LUMERIIX/FrequencyCounter/Documentation/Images/20180112_162158_HDR.jpg

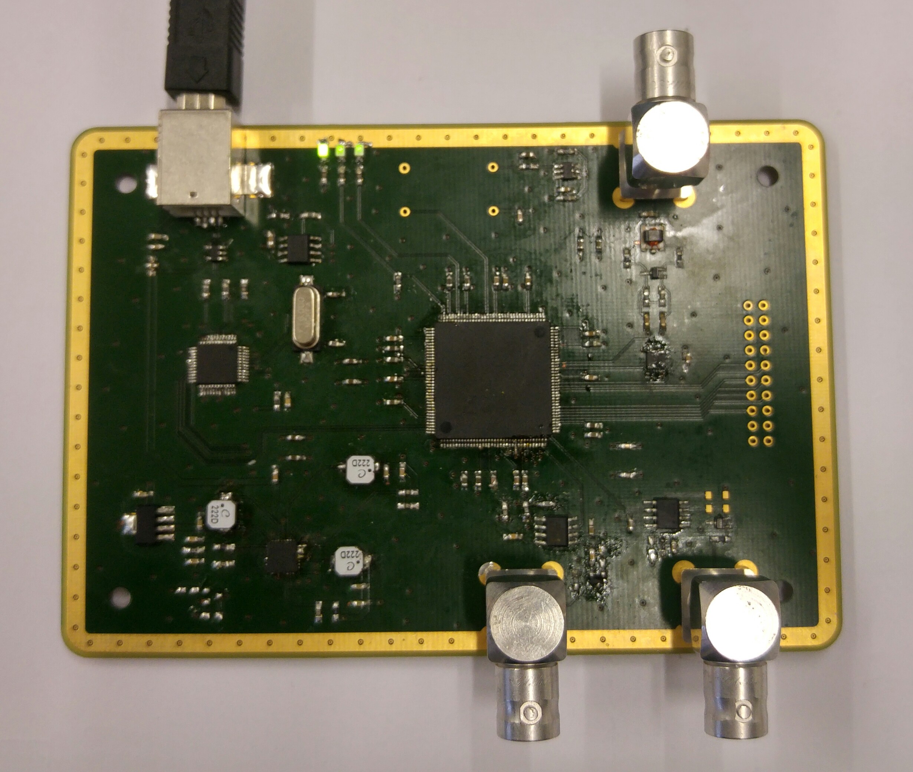
Documentation/Images/20180112_162158_HDR.jpg
