LUMERIIX/FrequencyCounter/Documentation/Images/20180112_162215_HDR.jpg

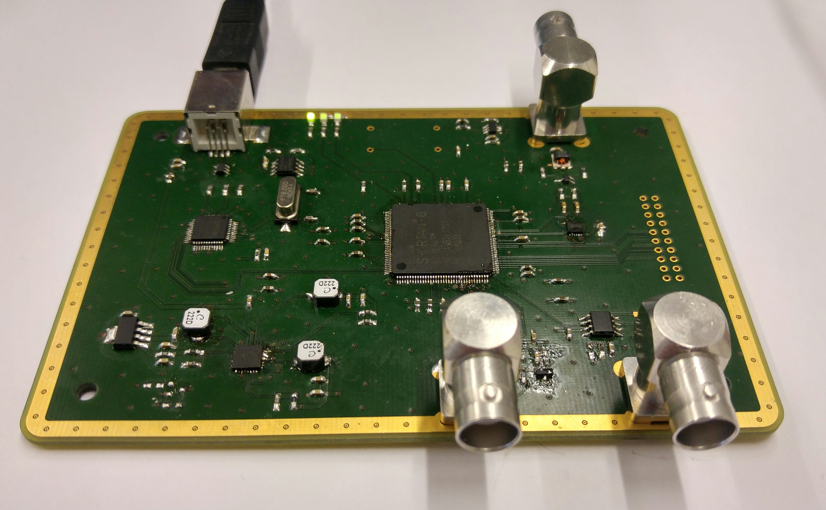
Documentation/Images/20180112_162215_HDR.jpg
