LUMERIIX/FrequencyCounter/Documentation/Images/20180112_162243_HDR.jpg

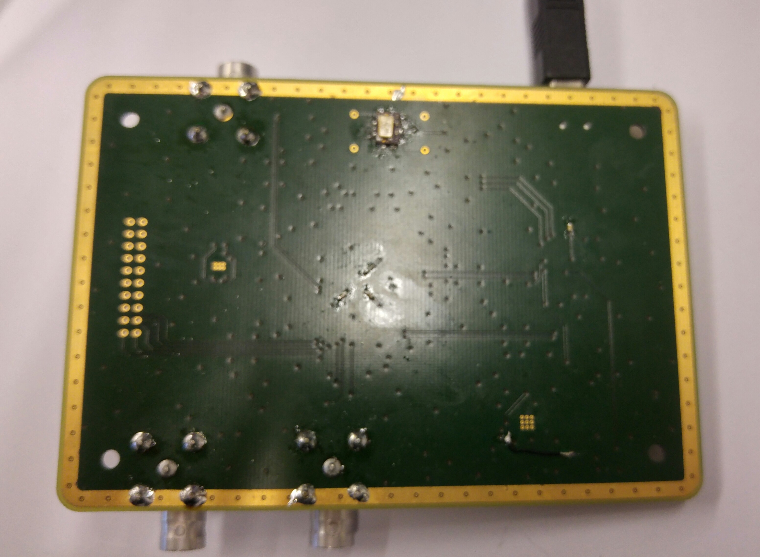
Documentation/Images/20180112_162243_HDR.jpg
