LUMERIIX/FrequencyCounter/Documentation/Images/Front.jpg

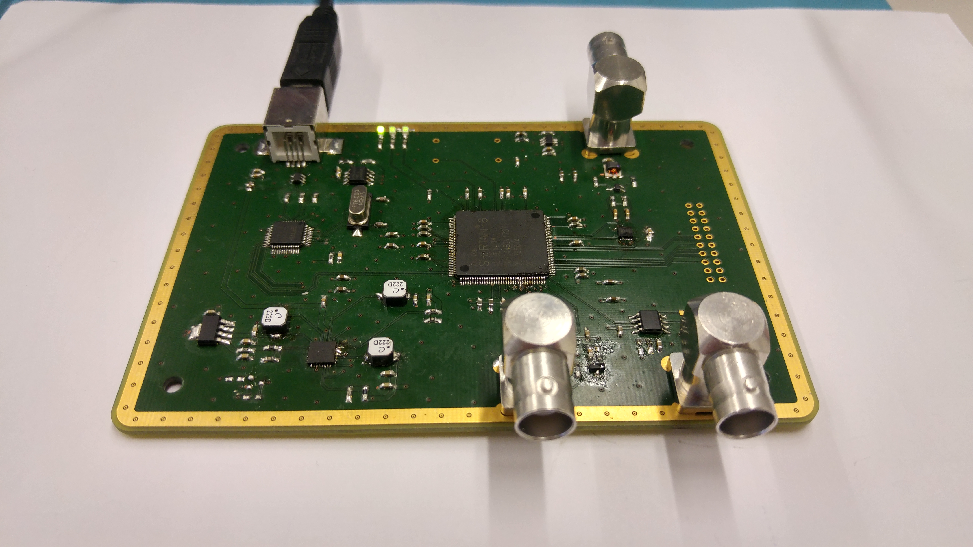
Documentation/Images/Front.jpg
