LUMERIIX/FrequencyCounter/Documentation/Images/Top.jpg

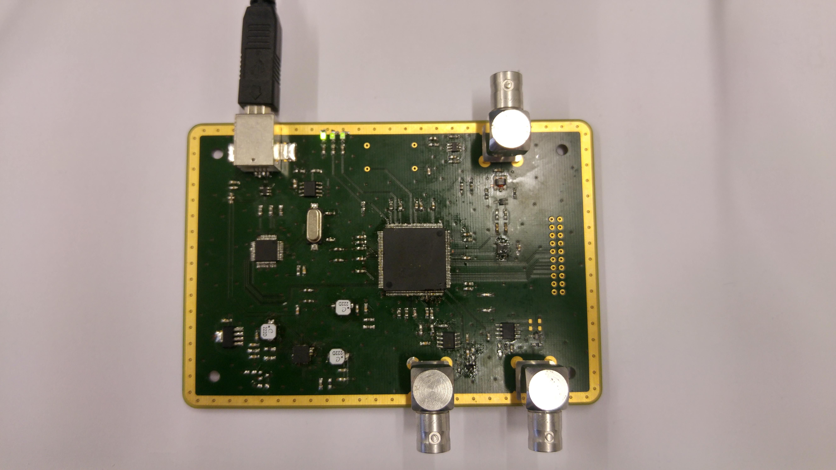
Documentation/Images/Top.jpg
