LUMERIIX/FrequencyCounter/VHDL/dualport_ram.vhd

library ieee;
use ieee.std_logic_1164.all;
use ieee.numeric_std.all;


library work;
use work.zpupkg.all;
entity dualport_ram is

    generic(
        wordPower       : integer;
        maxAddrBitBRAM  : integer
    );
    port(
        clk             : in  std_logic;
        memAWriteEnable : in  std_logic;
        memAAddr        : in  std_logic_vector(maxAddrBitBRAM downto wordPower-3);
        memAWrite       : in  std_logic_vector(2**wordPower-1 downto 0);
        memARead        : out std_logic_vector(2**wordPower-1 downto 0);
        memBWriteEnable : in  std_logic;
        memBAddr        : in  std_logic_vector(maxAddrBitBRAM downto wordPower-3);
        memBWrite       : in  std_logic_vector(2**wordPower-1 downto 0);
        memBRead        : out std_logic_vector(2**wordPower-1 downto 0)
    );
end dualport_ram;

architecture dualport_ram_arch of dualport_ram is


    type ram_type is array(natural range 0 to ((2**(maxAddrBitBRAM+1))/4)-1) of std_logic_vector(2**wordPower-1 downto 0); 

    shared variable ram : ram_type :=
    (
             0 => x"0b0b0b9b",
             1 => x"e0040000",
             2 => x"00000000",
             3 => x"00000000",
             4 => x"00000000",
             5 => x"00000000",
             6 => x"00000000",
             7 => x"00000000",
             8 => x"0b0b0b89",
             9 => x"8f040000",
            10 => x"00000000",
            11 => x"00000000",
            12 => x"00000000",
            13 => x"00000000",
            14 => x"00000000",
            15 => x"00000000",
            16 => x"71fd0608",
            17 => x"72830609",
            18 => x"81058205",
            19 => x"832b2a83",
            20 => x"ffff0652",
            21 => x"04000000",
            22 => x"00000000",
            23 => x"00000000",
            24 => x"71fd0608",
            25 => x"83ffff73",
            26 => x"83060981",
            27 => x"05820583",
            28 => x"2b2b0906",
            29 => x"7383ffff",
            30 => x"0b0b0b0b",
            31 => x"83a70400",
            32 => x"72098105",
            33 => x"72057373",
            34 => x"09060906",
            35 => x"73097306",
            36 => x"070a8106",
            37 => x"53510400",
            38 => x"00000000",
            39 => x"00000000",
            40 => x"72722473",
            41 => x"732e0753",
            42 => x"51040000",
            43 => x"00000000",
            44 => x"00000000",
            45 => x"00000000",
            46 => x"00000000",
            47 => x"00000000",
            48 => x"71737109",
            49 => x"71068106",
            50 => x"30720a10",
            51 => x"0a720a10",
            52 => x"0a31050a",
            53 => x"81065151",
            54 => x"53510400",
            55 => x"00000000",
            56 => x"72722673",
            57 => x"732e0753",
            58 => x"51040000",
            59 => x"00000000",
            60 => x"00000000",
            61 => x"00000000",
            62 => x"00000000",
            63 => x"00000000",
            64 => x"00000000",
            65 => x"00000000",
            66 => x"00000000",
            67 => x"00000000",
            68 => x"00000000",
            69 => x"00000000",
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
            96 => x"72722aff",
            97 => x"739f062a",
            98 => x"0974090a",
            99 => x"8106ff05",
           100 => x"06075351",
           101 => x"04000000",
           102 => x"00000000",
           103 => x"00000000",
           104 => x"71715351",
           105 => x"020d0406",
           106 => x"73830609",
           107 => x"81058205",
           108 => x"832b0b2b",
           109 => x"0772fc06",
           110 => x"0c515104",
           111 => x"00000000",
           112 => x"72098105",
           113 => x"72050970",
           114 => x"81050906",
           115 => x"0a810653",
           116 => x"51040000",
           117 => x"00000000",
           118 => x"00000000",
           119 => x"00000000",
           120 => x"72098105",
           121 => x"72050970",
           122 => x"81050906",
           123 => x"0a098106",
           124 => x"53510400",
           125 => x"00000000",
           126 => x"00000000",
           127 => x"00000000",
           128 => x"71098105",
           129 => x"52040000",
           130 => x"00000000",
           131 => x"00000000",
           132 => x"00000000",
           133 => x"00000000",
           134 => x"00000000",
           135 => x"00000000",
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
          1055 => x"00000000",
          1056 => x"00000000",
          1057 => x"00000000",
          1058 => x"00000000",
          1059 => x"00000000",
          1060 => x"00000000",
          1061 => x"00000000",
          1062 => x"00000000",
          1063 => x"00000000",
          1064 => x"00000000",
          1065 => x"00000000",
          1066 => x"00000000",
          1067 => x"00000000",
          1068 => x"00000000",
          1069 => x"00000000",
          1070 => x"00000000",
          1071 => x"00000000",
          1072 => x"00000000",
          1073 => x"00000000",
          1074 => x"00000000",
          1075 => x"00000000",
          1076 => x"00000000",
          1077 => x"00000000",
          1078 => x"00000000",
          1079 => x"00000000",
          1080 => x"00000000",
          1081 => x"00000000",
          1082 => x"00000000",
          1083 => x"00000000",
          1084 => x"00000000",
          1085 => x"00000000",
          1086 => x"00000000",
          1087 => x"00000000",
          1088 => x"00000000",
          1089 => x"00000000",
          1090 => x"00000000",
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
          1228 => x"ffffffff",
          1229 => x"00000000",
          1230 => x"ffffffff",
          1231 => x"00000000",
          1232 => x"00000000",

        others => x"00000000"
    );

begin
    process (clk) begin
        if (clk'event and clk = '1') then
            if (memAWriteEnable = '1') and (memBWriteEnable = '1') and (memAAddr=memBAddr) and (memAWrite/=memBWrite) then
                report "write collision" severity failure;
            end if;

            if (memAWriteEnable = '1') then
                ram(to_integer(unsigned(memAAddr))) := memAWrite;
                memARead <= memAWrite;
            else
                memARead <= ram(to_integer(unsigned(memAAddr)));
            end if;
        end if;
    end process;

    process (clk) begin
        if (clk'event and clk = '1') then
            if (memBWriteEnable = '1') then
                ram(to_integer(unsigned(memBAddr))) := memBWrite;
                memBRead <= memBWrite;
            else
                memBRead <= ram(to_integer(unsigned(memBAddr)));
            end if;
        end if;
    end process;



end dualport_ram_arch;
