LUMERIIX/FrequencyCounter/VHDL/FrequencyCounter_core.vhd

----------------------------------------------------------------------------------
-- Company:
-- Engineer: LJ
--
-- Create Date:    11:38:06 07/21/2017
-- Design Name:
-- Module Name: FrequencyCounter_core
-- Project Name: FrequencyCounter_core
-- Target Devices: iCE40
-- Tool versions:
-- Description:
--
-- Revision:
-- Revision 0.01 - File Created
-- Additional Comments:
--
----------------------------------------------------------------------------------
library IEEE;
use IEEE.STD_LOGIC_1164.ALL;
--use IEEE.STD_LOGIC_ARITH.ALL;
--use IEEE.STD_LOGIC_UNSIGNED.ALL;
use IEEE.NUMERIC_STD.ALL;

entity FrequencyCounter_core is
	port (
		CLK 			: in STD_LOGIC;
		MEAS_CLK		: in STD_LOGIC;
		GateEnable	 	: in STD_LOGIC;
		CounterReset    : in STD_LOGIC;
		RefCountVal		: out std_logic_vector (31 downto 0);
		GatePulse		: in  STD_LOGIC;
		TEST 			: out STD_LOGIC;
		MeasCountVal	: out std_logic_vector (31 downto 0);
		OpenGate		: out STD_LOGIC;
		DataValid		: out STD_LOGIC;
		RESET			: in STD_LOGIC;
		Valid 			: in STD_LOGIC
		);
end FrequencyCounter_core;

architecture structure of FrequencyCounter_core is

	component Counter is
		port(
		CLK 		: in STD_LOGIC;
		ENABLE 		: in STD_LOGIC;
		TEST		: out STD_LOGIC;
		DataValid	: out STD_LOGIC;
		RESET		: in STD_LOGIC;
		DATA		: out std_logic_vector(31 downto 0)
		);
	end component Counter;
	signal OpenGate_s : STD_LOGIC := '0';
	signal RefCountVal_s : unsigned (31 downto 0) := to_unsigned(0,32);
	signal MeasCountVal_s : unsigned (31 downto 0) := to_unsigned(0,32);
	signal DataValidRef_s : STD_LOGIC := '0';
	signal DataValidMeas_s : STD_LOGIC := '0';
	signal DataValid_s : STD_LOGIC := '0';
begin
	DataValid_s <= DataValidMeas_s and DataValidRef_s;
	--RefCountVal <= RefCountVal_s;
	--MeasCountVal <= MeasCountVal_s;
	OpenGate <= OpenGate_s;
	DataValid <= DataValid_s;

    Init : process (RESET)
	begin
        if rising_edge (RESET) then
            --OpenGate_s <= '0';
            --ountVal_s <= to_unsigned(0,RefCountVal_s'length);
            --MeasCountVal_s <= to_unsigned(0,MeasCountVal_s'length);
            --DataValidRef_s <= '0';
            --DataValidMeas_s <= '0';
            --DataValid_s <= '0';
        end if;
	end process;

	GateControl : process (MEAS_CLK) begin
		if rising_edge (MEAS_CLK)  then
			if GateEnable = '1' and Valid = '0' then
				OpenGate_s <= '1';
			end if;
			if Valid = '1' and GatePulse = '0' then
				OpenGate_s <= '0';
			end if;
		end if;
	end process;

	BaseCounter : component Counter
	port map(
		CLK => CLK,
		ENABLE => OpenGate_s,
		TEST => open,
		DataValid => DataValidRef_s,
		RESET => CounterReset,
		DATA => RefCountVal
	);

	MeasCounter : component Counter
	port map(
		CLK => MEAS_CLK,
		ENABLE => OpenGate_s,
		TEST => open,
		DataValid => DataValidMeas_s,
		RESET => CounterReset,
		DATA => MeasCountVal
	);
end architecture structure;
